Saketspradhan/Autonomous-Vehicle-Steering-using-YOLO-4/circuits/arduino_uno_extension.jpeg

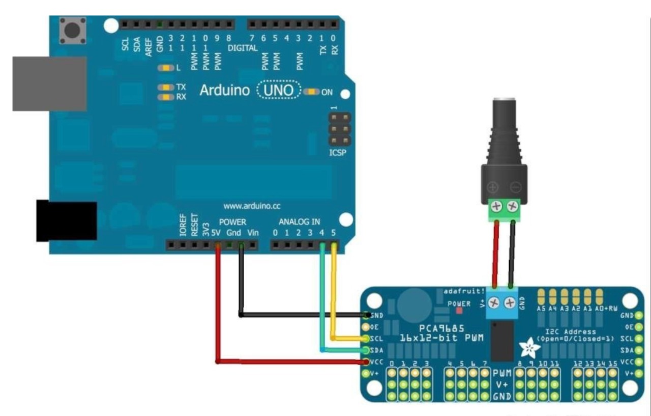
circuits/arduino_uno_extension.jpeg
