Saketspradhan/Autonomous-Vehicle-Steering-using-YOLO-4/circuits/dc_motors_with_driver.jpeg

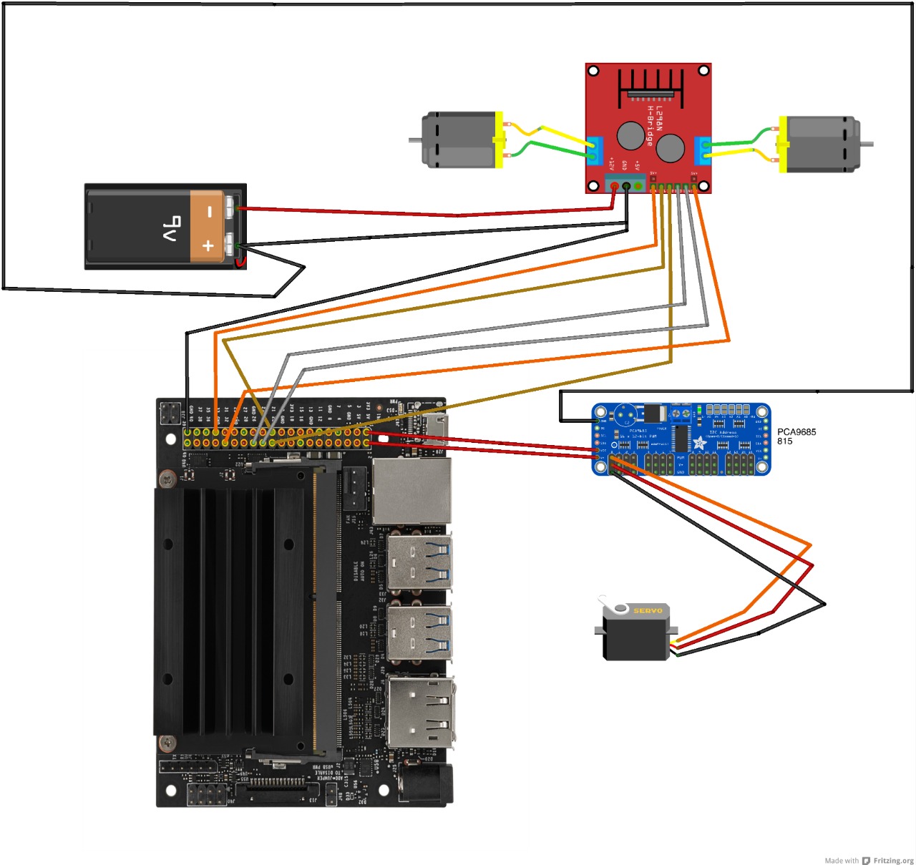
circuits/dc_motors_with_driver.jpeg
