Saketspradhan/Autonomous-Vehicle-Steering-using-YOLO-4/circuits/steering_design.jpeg

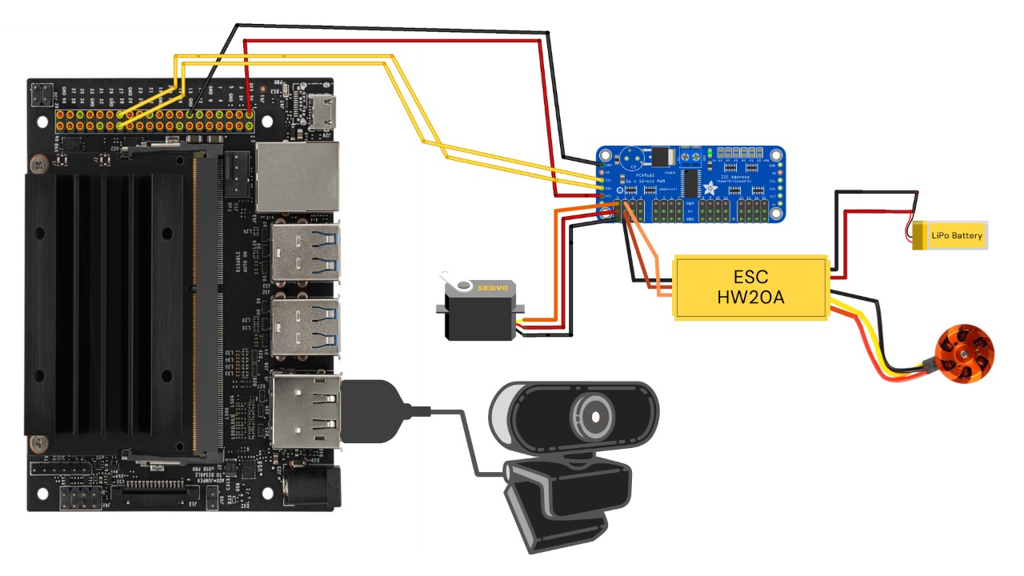
circuits/steering_design.jpeg
