Saketspradhan/Autonomous-Vehicle-Steering-using-YOLO-4/design/design_files/front-chassis.stl

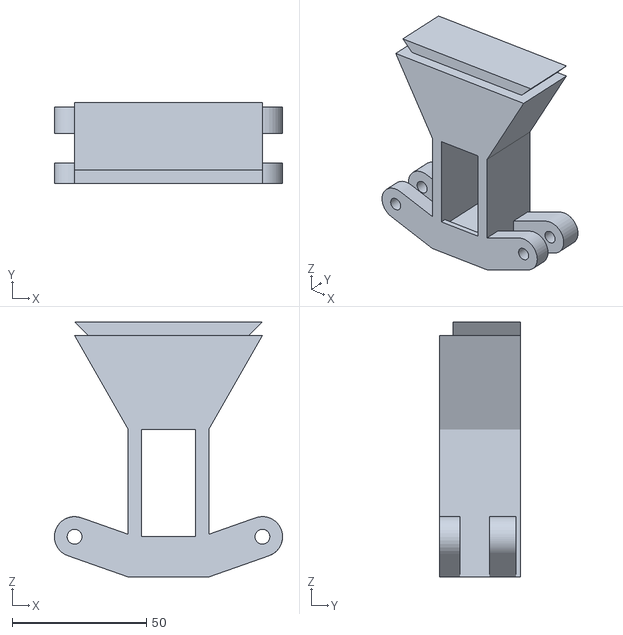
[picture p30: CAD file, 2024-01-29]
design/design_files/front-chassis.stl
85.0 x 30.0 x 95.0
