Saketspradhan/Autonomous-Vehicle-Steering-using-YOLO-4/design/design_files/spur-gear-gearbox.stl

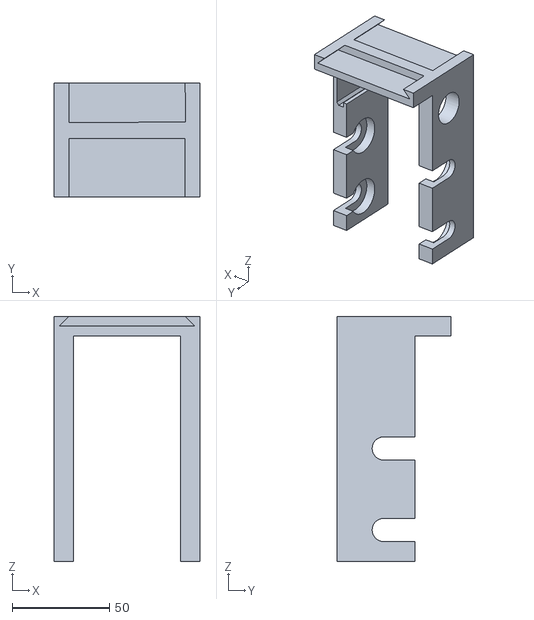
[picture p31: CAD file, 2024-01-29]
design/design_files/spur-gear-gearbox.stl
75.0 x 58.5 x 126.2
