Saketspradhan/Autonomous-Vehicle-Steering-using-YOLO-4/design/design_files/back-axle.stl

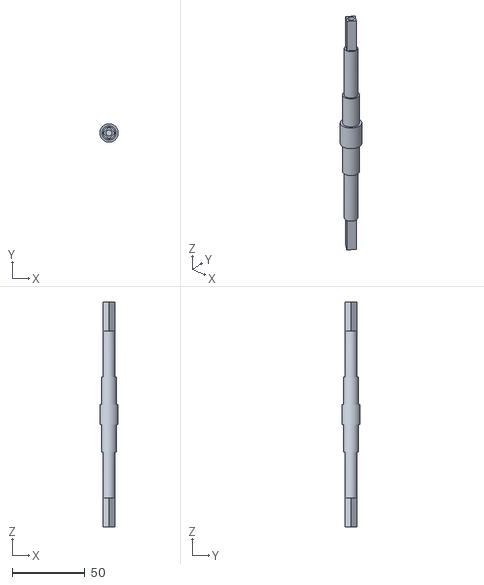
[picture p32: CAD file, 2024-01-29]
design/design_files/back-axle.stl
12.7 x 12.7 x 155.0
