Saketspradhan/Autonomous-Vehicle-Steering-using-YOLO-4/design/design_files/B1-gear-16 tooth.stl

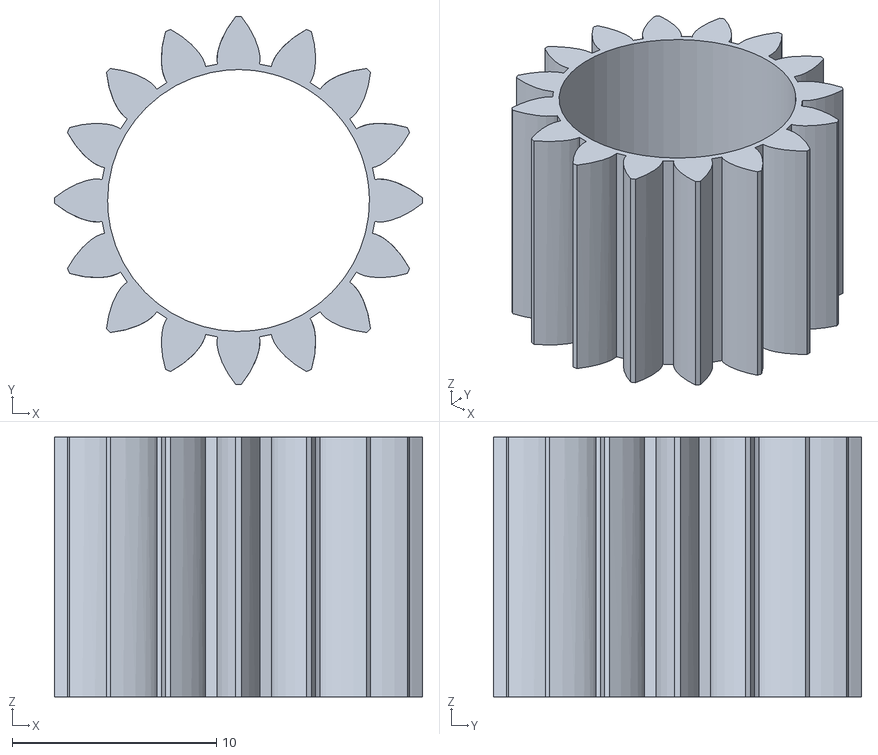
[picture p33: CAD file, 2024-01-29]
design/design_files/B1-gear-16 tooth.stl
18.0 x 18.0 x 12.7
