Saketspradhan/Autonomous-Vehicle-Steering-using-YOLO-4/results/path_estimation_snapshot_#frame5578.jpeg

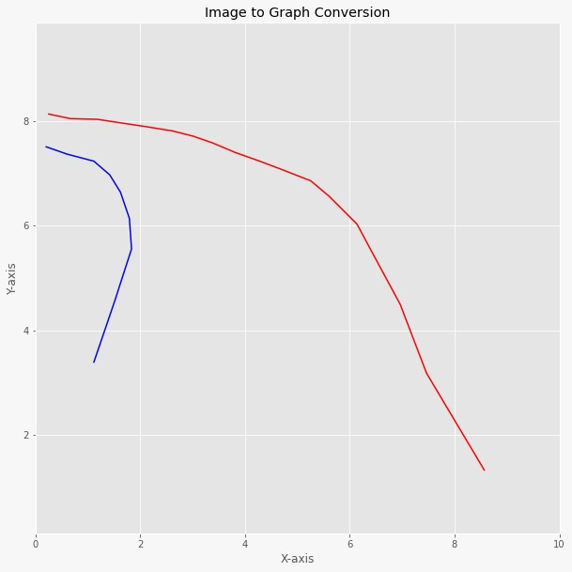
results/path_estimation_snapshot_#frame5578.jpeg
